jdodgen/cruise-line-shower-grab-handle-tray/src/stl/tray_shortmount.stl

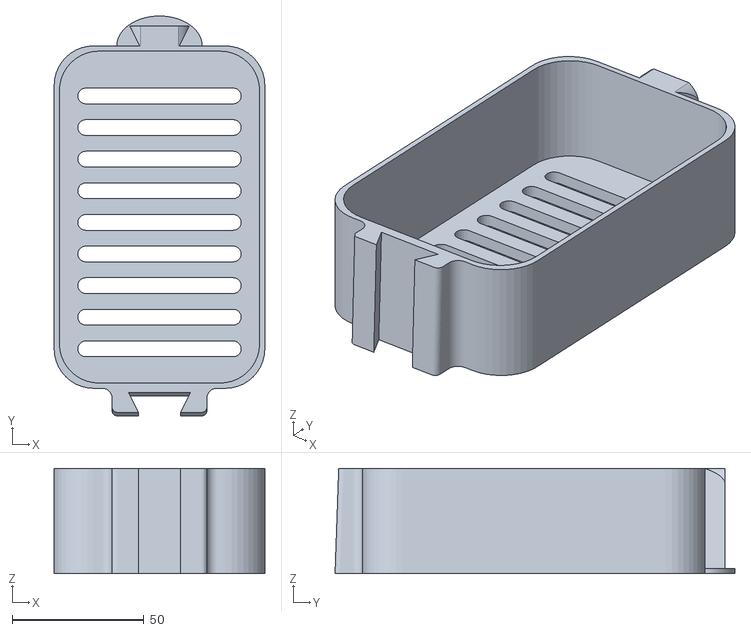
[picture p15: CAD file, 2025-01-03]
src/stl/tray_shortmount.stl
80.0 x 151.8 x 40.0
