jdodgen/cruise-line-shower-grab-handle-tray/stl/180mm_mount_tray.stl

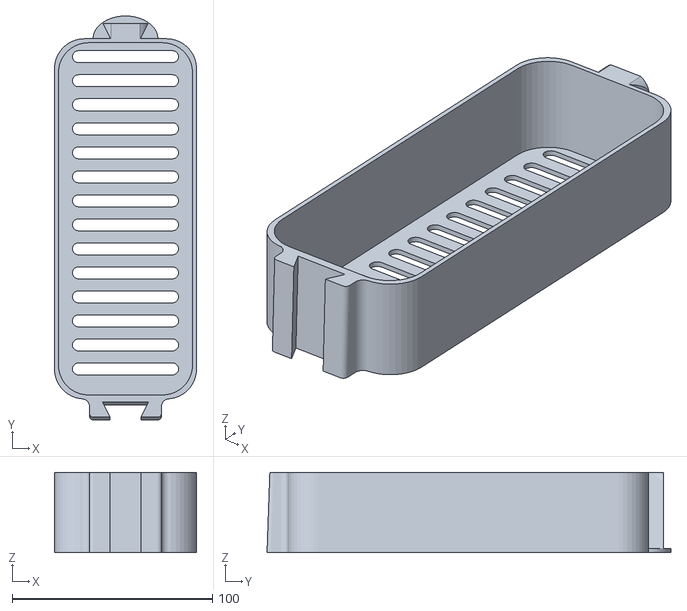
[picture p16: CAD file, 2025-03-28]
stl/180mm_mount_tray.stl
71.0 x 201.8 x 40.0
