jdodgen/cruise-line-shower-grab-handle-tray/src/stl/tray_loop.stl

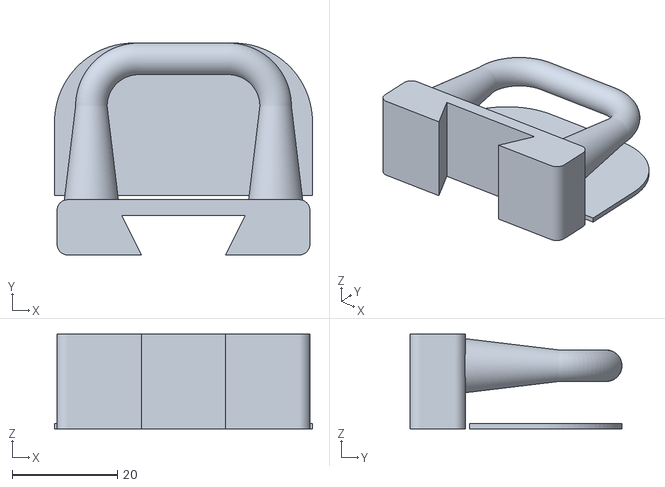
[picture p17: CAD file, 2025-01-03]
src/stl/tray_loop.stl
49.0 x 40.2 x 18.0
