jdodgen/cruise-line-shower-grab-handle-tray/stl/20mm_mount.stl

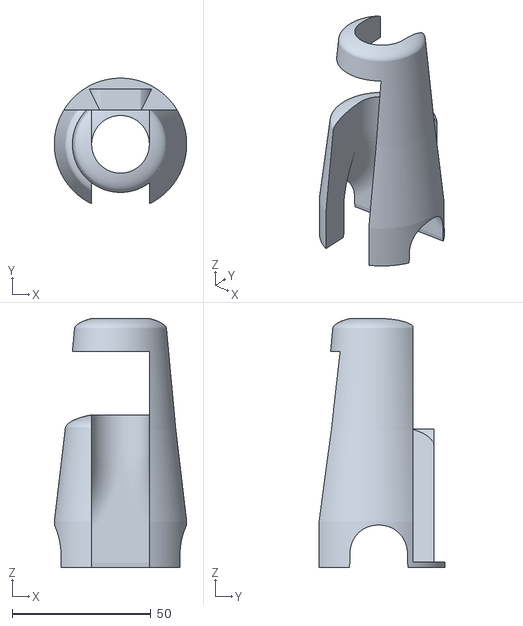
[picture p18: CAD file, 2025-03-28]
stl/20mm_mount.stl
47.8 x 45.4 x 89.9
