jdodgen/cruise-line-shower-grab-handle-tray/src/stl/tray_long.stl

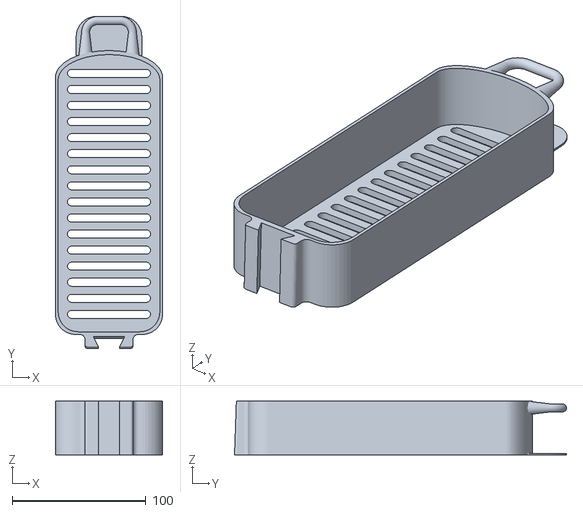
[picture p19: CAD file, 2025-01-03]
src/stl/tray_long.stl
80.0 x 248.0 x 40.0
