jdodgen/cruise-line-shower-grab-handle-tray/stl/25x50mm_mount.stl

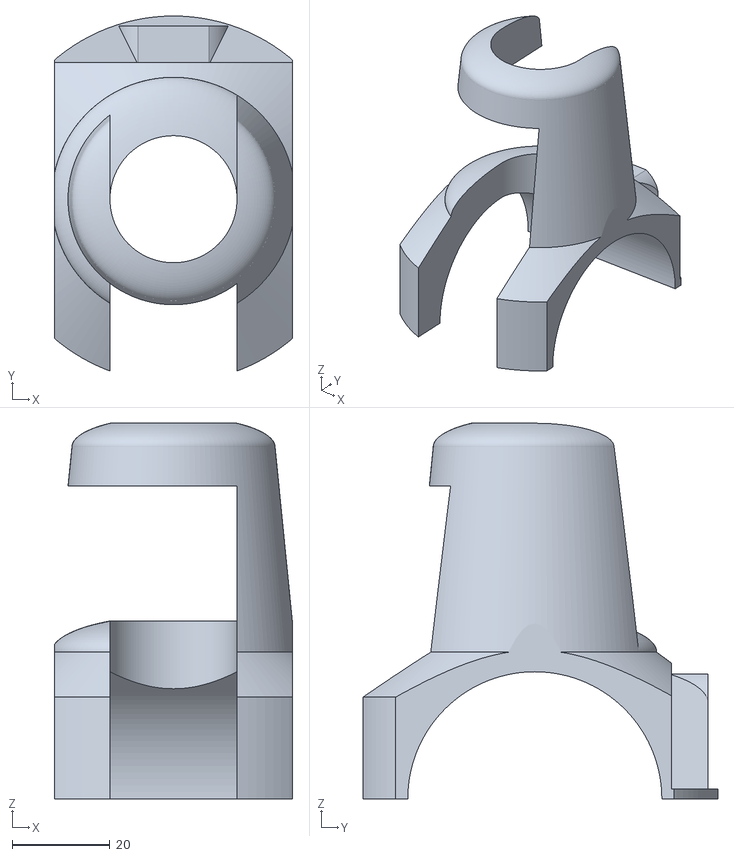
[picture p20: CAD file, 2025-03-28]
stl/25x50mm_mount.stl
48.8 x 72.7 x 76.9
