jdodgen/cruise-line-shower-grab-handle-tray/src/stl/tray_short.stl

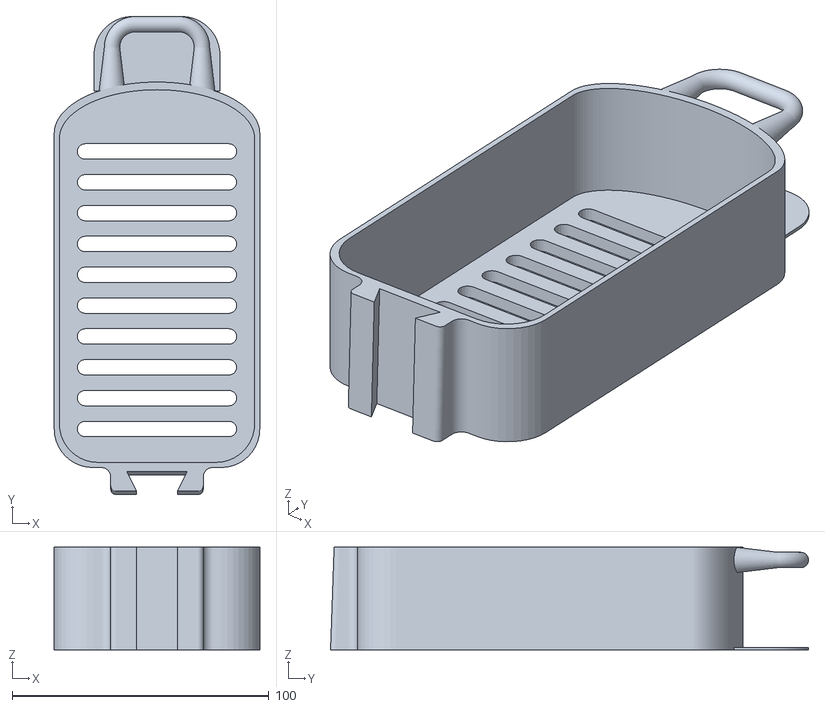
[picture p21: CAD file, 2025-01-03]
src/stl/tray_short.stl
80.0 x 186.0 x 40.0
