jdodgen/cruise-line-shower-grab-handle-tray/src/stl/dovetail.stl

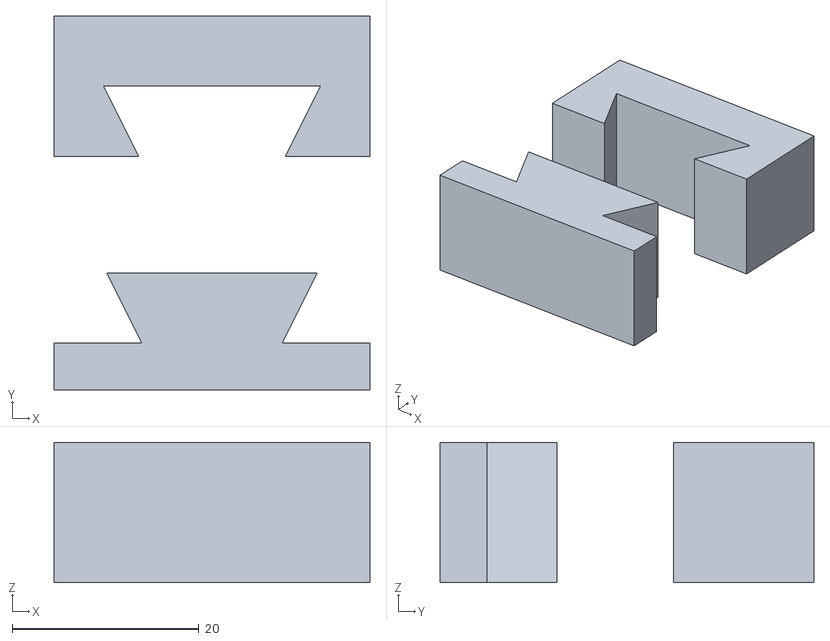
[picture p22: CAD file, 2024-12-15]
src/stl/dovetail.stl
33.8 x 40.0 x 15.0
